dgorbunov/SpatialSense/photos/case1.png

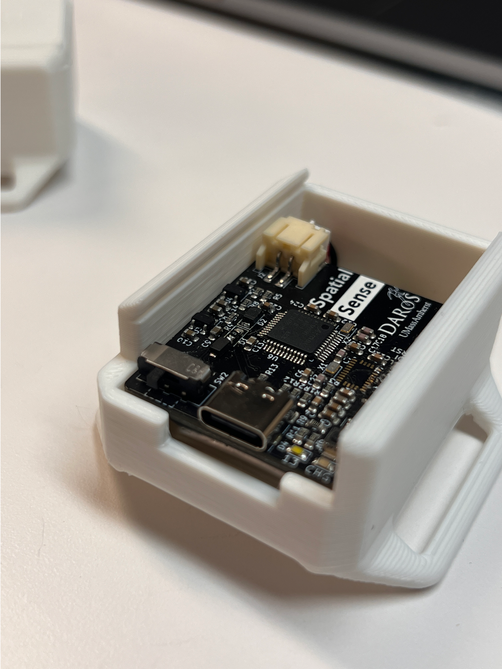
photos/case1.png
